dawidilba/Eagle_LTSpice_Projekt_G-o-nik_BT/LTSpice/Przetwornica24V.asc

C1: cap; 120p
C2: cap; 4.7µ
C3: cap; 2.2µ
D1: schottky
L1: ind; 10µ
R1: res; 51k
R2: res; 180k
R3: res; 10k
U1: LM27313_TRANS
V1: voltage; 12
Named nets: Vin, 0, Vout
.tran 300u
