dawidilba/Eagle_LTSpice_Projekt_G-o-nik_BT/LTSpice/TPA3132.asc

C1: cap; 1µ
C2: cap; 0.68µ
C3: cap; 0.68µ
C4: cap; 0.68µ
C5: cap; 0.68µ
C6: cap; 1µ
C7: cap; 1µ
C8: cap; 1µ
C9: cap; 1µ
C10: cap; 0.01µ
C11: cap; 0.01µ
C12: cap; 0.01µ
C13: cap; 0.01µ
L1: ind; 10µ
L2: ind; 10µ
L3: ind; 10µ
L4: ind; 10µ
R1: res; 100k
R2: res; 20k
R3: res; 3.3
R4: res; 3.3
R5: res; 100k
R6: res; 3.3
R7: res; 3.3
R8: res; 4
R9: res; 4
U1: TPA3132D2_AVG
V1: voltage; 24
V2: voltage; SINE(0 1 1000)
V3: voltage; SINE(0 1 1000)
Named nets: PLIMIT, 0, VCC, INL+, INR+, OutL, OutR
.tran 0 5ms 0 0.1ms
